PetyC/H7-Mode/2.Firmware/LVGL/CoreH7/import/WIFI_discon.png

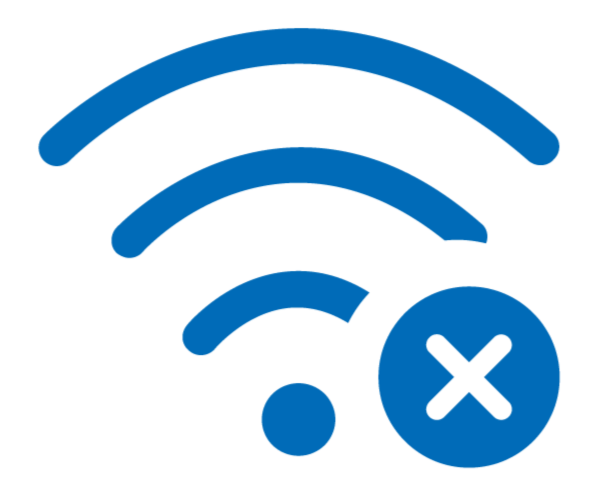
2.Firmware/LVGL/CoreH7/import/WIFI_discon.png
