PetyC/H7-Mode/1.Hardware/PCB_3D/STEP/1612_26MHZ.STEP

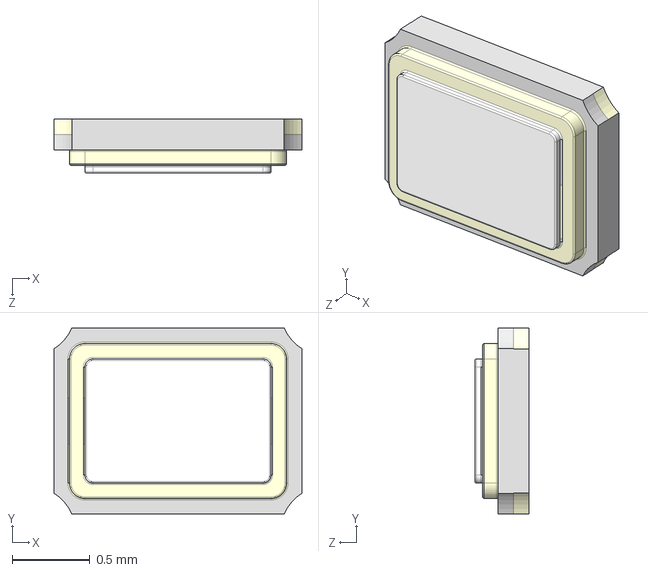
[picture p30: CAD file, 2022-08-18]
1.Hardware/PCB_3D/STEP/1612_26MHZ.STEP
1.60 x 1.20 x 0.35 mm
