PetyC/H7-Mode/1.Hardware/PCB_3D/STEP/MSK12C02.STEP

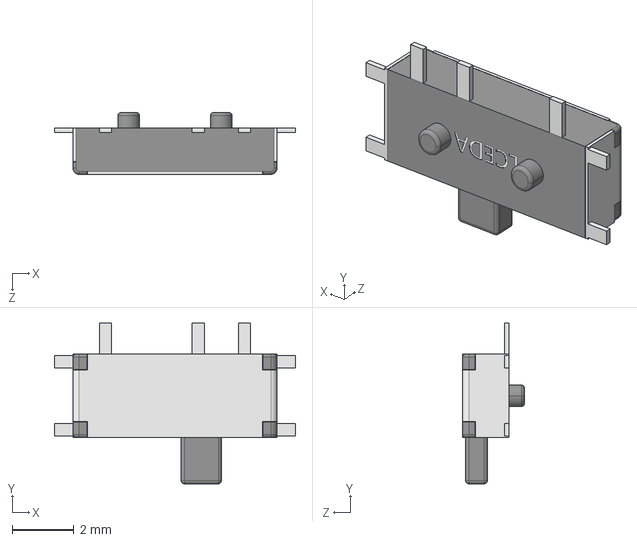
[picture p31: CAD file, 2022-08-18]
1.Hardware/PCB_3D/STEP/MSK12C02.STEP
7.80 x 5.20 x 2.00 mm
