PetyC/H7-Mode/1.Hardware/PCB_3D/STEP/K3-2410S-F1.STEP

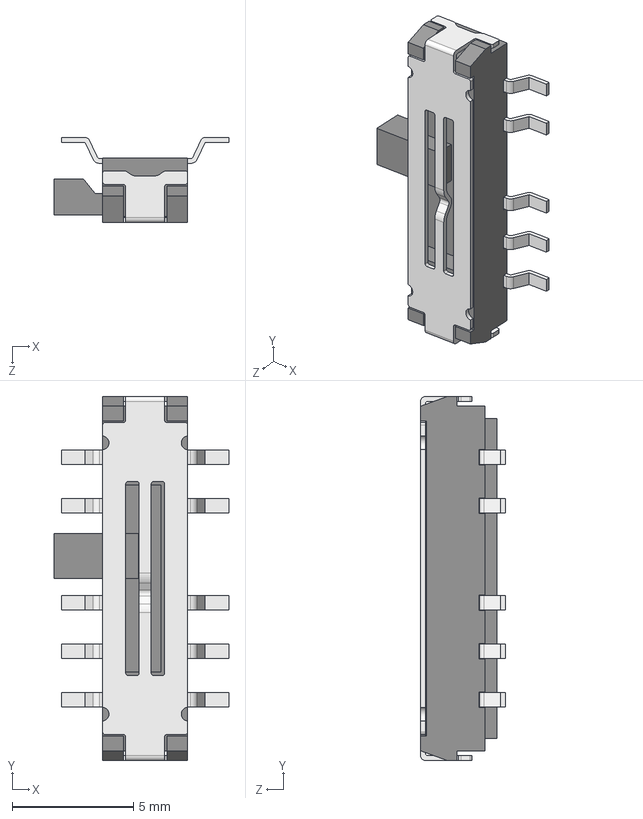
[picture p32: CAD file, 2022-08-18]
1.Hardware/PCB_3D/STEP/K3-2410S-F1.STEP
7.20 x 15.0 x 3.50 mm
