PetyC/H7-Mode/1.Hardware/PCB_3D/STEP/TM-2023.STEP

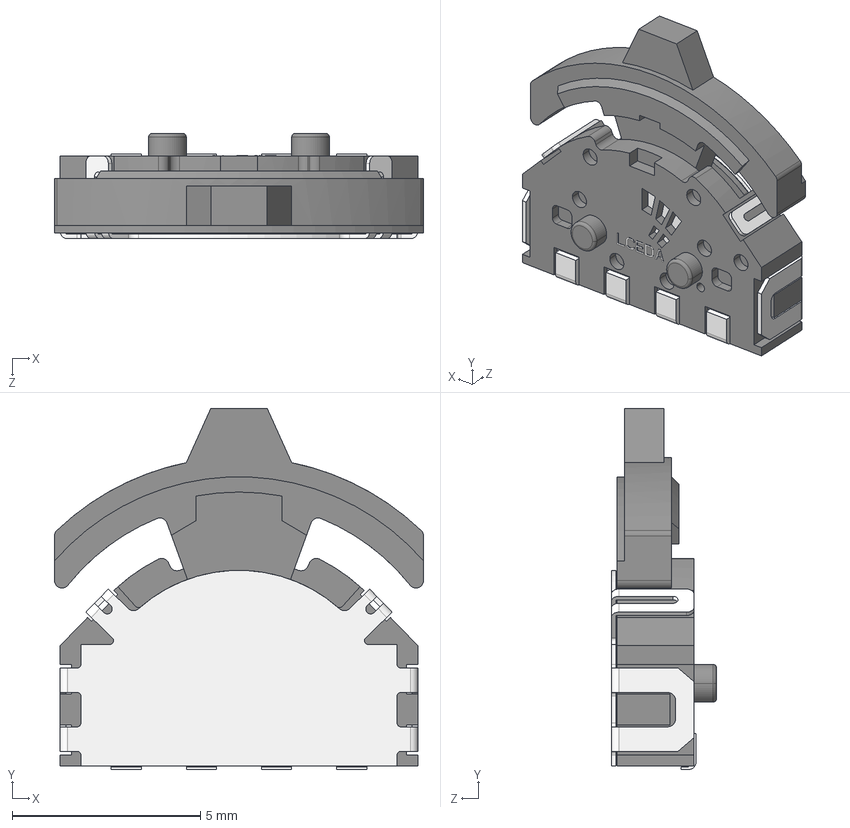
[picture p33: CAD file, 2022-08-18]
1.Hardware/PCB_3D/STEP/TM-2023.STEP
9.80 x 9.59 x 2.80 mm
