PetyC/H7-Mode/2.Firmware/STM32H743_FreeRTOS/User/Driver/src/Bsp_w25qxx.c

#include "Bsp_w25qxx.h"

/* 内部使用函数 */
static void QSPI_W25Qx_Write_Enable(QSPI_HandleTypeDef *hqspi);
static uint8_t QSPI_W25Qx_AutoPollingMemRead(QSPI_HandleTypeDef *hqspi);
static void Flash_Error_Handler(void);

/* 内部使用变量 */
struct 
{
  uint8_t CMD_Finished;     //命令发送状态 1:完成 0:未完成
  uint8_t RX_Finished;      //RX接受状态 1:完成 0:未完成
  uint8_t TX_Finished;      //TX发送状态 1:完成 0:未完成
  uint8_t Flash_Finished;   //FLASH状态 1:完成 0:未完成
}static __IO FLASH_Status;


/**
 * @brief 初始化W25QXX
 * @param {*}
 * @return {uint8_t} 0:成功  1:失败
 */
uint8_t QSPI_W25Qx_Init(void)
{	
	uint32_t FLASH_ID = 0;
	uint32_t FLASH_Type = 0;
	
	QSPI_W25Qx_Reset_Memory();
 
	FLASH_ID = QSPI_W25Qx_ReadID();
	FLASH_Type = QSPI_W25Qx_Read_Type();

	if(FLASH_ID == 0XEF4018 && FLASH_Type == 0XEF17)
	{
		return 0;
	}
	else
	{
		return 1;
	}
	
}


/**
 * @brief 读取外部FLASH的型号  (使用SPI模式的指令)
 * @param {*}
 * @return {uint32_t}  FLASH的ID
 */
uint32_t QSPI_W25Qx_Read_Type(void)
{
	uint32_t Type;

	QSPI_CommandTypeDef s_command = {0};
	uint8_t buf[3];

	/* 基本配置 */
	s_command.InstructionMode = QSPI_INSTRUCTION_1_LINE;	 // 1线方式发送指令
	s_command.AddressSize = QSPI_ADDRESS_24_BITS;			 // 24位地址
	s_command.AlternateByteMode = QSPI_ALTERNATE_BYTES_NONE; //无交替字节
	s_command.DdrMode = QSPI_DDR_MODE_DISABLE;				 // W25Q128JV不支持DDR模式
	s_command.DdrHoldHalfCycle = QSPI_DDR_HHC_ANALOG_DELAY;	 // DDR模式，数据输出延迟
	s_command.SIOOMode = QSPI_SIOO_INST_EVERY_CMD;			 //每次传输都发指令

	/* 读取JEDEC ID */
	s_command.Instruction = READ_ID_CMD; 	//读取命令: 0x90
	s_command.AddressMode = QSPI_ADDRESS_1_LINE; //没有地址
	s_command.DataMode = QSPI_DATA_1_LINE;	   // 1线数据
	s_command.DummyCycles = 0;				   //无空周期
	s_command.NbData = 2;					   //读取三个数据

	/* 发送指令 */
	if (HAL_QSPI_Command(&HQSPI_HANDLE, &s_command, HAL_QPSI_TIMEOUT_DEFAULT_VALUE) != HAL_OK)
	{
		Flash_Error_Handler();
	}

	/* 启动接收 */
	if (HAL_QSPI_Receive(&HQSPI_HANDLE, buf, HAL_QPSI_TIMEOUT_DEFAULT_VALUE) != HAL_OK)
	{
		Flash_Error_Handler();
	}

	Type = (buf[0] << 8) | buf[1];
	
	return Type;
}



/**
 * @brief 读取外部FLASH的ID  (使用SPI模式的指令)
 * @param {*}
 * @return {uint32_t}  FLASH的ID
 */
uint32_t QSPI_W25Qx_ReadID(void)
{
	uint32_t uiID;

	QSPI_CommandTypeDef s_command = {0};
	uint8_t buf[3];

	/* 基本配置 */
	s_command.InstructionMode = QSPI_INSTRUCTION_1_LINE;	 // 1线方式发送指令
	s_command.AddressSize = QSPI_ADDRESS_24_BITS;			 // 24位地址
	s_command.AlternateByteMode = QSPI_ALTERNATE_BYTES_NONE; //无交替字节
	s_command.DdrMode = QSPI_DDR_MODE_DISABLE;				 // W25Q128JV不支持DDR模式
	s_command.DdrHoldHalfCycle = QSPI_DDR_HHC_ANALOG_DELAY;	 // DDR模式，数据输出延迟
	s_command.SIOOMode = QSPI_SIOO_INST_EVERY_CMD;			 //每次传输都发指令

	/* 读取JEDEC ID */
	s_command.Instruction = READ_JEDEC_ID_CMD; //读取ID命令: 0x9F
	s_command.AddressMode = QSPI_ADDRESS_NONE; //没有地址
	s_command.DataMode = QSPI_DATA_1_LINE;	   // 1线数据
	s_command.DummyCycles = 0;				   //无空周期
	s_command.NbData = 3;					   //读取三个数据

	/* 发送指令 */
	if (HAL_QSPI_Command(&HQSPI_HANDLE, &s_command, HAL_QPSI_TIMEOUT_DEFAULT_VALUE) != HAL_OK)
	{
		Flash_Error_Handler();
	}

	/* 启动接收 */
	if (HAL_QSPI_Receive(&HQSPI_HANDLE, buf, HAL_QPSI_TIMEOUT_DEFAULT_VALUE) != HAL_OK)
	{
		Flash_Error_Handler();
	}

	uiID = (buf[0] << 16) | (buf[1] << 8) | buf[2];

	return uiID;
}

/**
 * @brief 复位外部Flash
 * @param {*}
 * @return {*}
 */
void QSPI_W25Qx_Reset_Memory(void)
{
	QSPI_CommandTypeDef s_command = {0};

	/* 基本配置 */
	s_command.InstructionMode = QSPI_INSTRUCTION_1_LINE;	 // 1线方式发送指令
	s_command.AddressSize = QSPI_ADDRESS_24_BITS;			 // 24位地址
	s_command.AlternateByteMode = QSPI_ALTERNATE_BYTES_NONE; //无交替字节
	s_command.DdrMode = QSPI_DDR_MODE_DISABLE;				 // W25Q128JV不支持DDR模式
	s_command.DdrHoldHalfCycle = QSPI_DDR_HHC_ANALOG_DELAY;	 // DDR模式，数据输出延迟
	s_command.SIOOMode = QSPI_SIOO_INST_EVERY_CMD;			 //每次传输都发指令

	/* 复位使能W25x */
	s_command.Instruction = RESET_ENABLE_CMD;  //复位使能命令
	s_command.AddressMode = QSPI_ADDRESS_NONE; //没有地址
	s_command.DataMode = QSPI_DATA_NONE;	   //没有数据
	s_command.DummyCycles = 0;				   //无空周期

	/* 发送复位使能命令 */
	if (HAL_QSPI_Command(&HQSPI_HANDLE, &s_command, HAL_QPSI_TIMEOUT_DEFAULT_VALUE) != HAL_OK)
	{
		Flash_Error_Handler();
	}

  /* 自动轮询模式等待等待完成 */
	if (QSPI_W25Qx_AutoPollingMemRead(&HQSPI_HANDLE) != HAL_OK)
	{
		Flash_Error_Handler();
	}

	/* 发送复位命令 */
	s_command.Instruction = RESET_MEMORY_CMD; //复位命令

	/* 发送复位使能命令 */
	if (HAL_QSPI_Command(&HQSPI_HANDLE, &s_command, HAL_QPSI_TIMEOUT_DEFAULT_VALUE) != HAL_OK)
	{
		Flash_Error_Handler();
	}

	/* 自动轮询模式等待等待完成 */
	if (QSPI_W25Qx_AutoPollingMemRead(&HQSPI_HANDLE) != HAL_OK)
	{
		Flash_Error_Handler();
	}
}

/**
 * @brief 擦除外部FLASH的扇区（大小：4KB)
 * @param {uint32_t} _sectorAddr 扇区地址，以4KB为单位的地址，比如0，4096，8192等
 * @return {*}
 */
void QSPI_W25Qx_EraseSector(uint32_t _sectorAddr)
{
	QSPI_CommandTypeDef s_command = {0};

	/* 写使能 */
	QSPI_W25Qx_Write_Enable(&HQSPI_HANDLE);

	/* 基本配置 */
	s_command.InstructionMode = QSPI_INSTRUCTION_1_LINE;	 // 1线方式发送指令
	s_command.AddressSize = QSPI_ADDRESS_24_BITS;			 // 24位地址
	s_command.AlternateByteMode = QSPI_ALTERNATE_BYTES_NONE; //无交替字节
	s_command.DdrMode = QSPI_DDR_MODE_DISABLE;				 // W25Q128JV不支持DDR模式
	s_command.DdrHoldHalfCycle = QSPI_DDR_HHC_ANALOG_DELAY;	 // DDR模式，数据输出延迟
	s_command.SIOOMode = QSPI_SIOO_INST_EVERY_CMD;			 //每次传输都发指令

	/* 擦除扇区配置 */
	s_command.Instruction = SECTOR_ERASE_CMD;	 //扇区擦除指令
	s_command.AddressMode = QSPI_ADDRESS_1_LINE; // 1线地址方式
	s_command.DataMode = QSPI_DATA_NONE;		 //没有数据
	s_command.Address = _sectorAddr;			 //扇区的首地址，保证是4KB整数倍
	s_command.DummyCycles = 0;					 //无空周期

 
  FLASH_Status.CMD_Finished = 0;

	/* 发送指令 */
	if (HAL_QSPI_Command_IT(&HQSPI_HANDLE, &s_command) != HAL_OK)
	{
		Flash_Error_Handler();
	}

	/* 等待命令发送完毕 */
	while (FLASH_Status.CMD_Finished == 0);
	FLASH_Status.CMD_Finished = 0;

	/* 等待擦写结束 */
	FLASH_Status.Flash_Finished = 0;
	QSPI_W25Qx_AutoPollingMemRead(&HQSPI_HANDLE);
	while (FLASH_Status.Flash_Finished == 0);
	FLASH_Status.Flash_Finished = 0;

	
}

/**
 * @brief 擦除整个芯片
 * @return {*}
 */
void QSPI_W25Qx_EraseChip(void)
{
	QSPI_CommandTypeDef s_command = {0};

	/* 写使能 */
	QSPI_W25Qx_Write_Enable(&HQSPI_HANDLE);

	/* 基本配置 */
	s_command.InstructionMode = QSPI_INSTRUCTION_1_LINE;	 // 1线方式发送指令
	s_command.AddressSize = QSPI_ADDRESS_24_BITS;			 // 24位地址
	s_command.AlternateByteMode = QSPI_ALTERNATE_BYTES_NONE; //无交替字节
	s_command.DdrMode = QSPI_DDR_MODE_DISABLE;				 // W25Q128JV不支持DDR模式
	s_command.DdrHoldHalfCycle = QSPI_DDR_HHC_ANALOG_DELAY;	 // DDR模式，数据输出延迟
	s_command.SIOOMode = QSPI_SIOO_INST_EVERY_CMD;			 //每次传输都发指令

	/* 擦除扇区配置 */
	s_command.Instruction = SECTOR_CHIP_CMD;	 //擦除整个芯片指令
	s_command.AddressMode = QSPI_ADDRESS_1_LINE; // 1线地址方式
	s_command.DataMode = QSPI_DATA_NONE;		 //没有数据
	s_command.Address = 0;			            //没有地址
	s_command.DummyCycles = 0;					 //无空周期

 
  FLASH_Status.CMD_Finished = 0;

	/* 发送指令 */
	if (HAL_QSPI_Command_IT(&HQSPI_HANDLE, &s_command) != HAL_OK)
	{
		Flash_Error_Handler();
	}

	/* 等待命令发送完毕 */
	while (FLASH_Status.CMD_Finished == 0);
	FLASH_Status.CMD_Finished = 0;

	/* 等待擦写结束 */
	FLASH_Status.Flash_Finished = 0;
	QSPI_W25Qx_AutoPollingMemRead(&HQSPI_HANDLE);
	while (FLASH_Status.Flash_Finished == 0);
	FLASH_Status.Flash_Finished = 0;

	
}


/**
 * @brief 连续读取若干字节，字节的个数不能超出芯片容量  (从SPI模式切换到QSPI模式，读取完毕后切换回SPI模式（其他函数仅仅支持SPI模式）。)
 * @param {uint8_t} *_pBuf 读取数据的存放地址
 * @param {uint32_t} _read_Addr 起始的地址
 * @param {uint32_t} _read_Size  数据个数，可以大于W25Q128JV_PAGE_SIZE,但不能超出芯片总容量
 * @return {*}
 */
void QSPI_W25Qx_Read_Buffer(uint32_t _read_Addr , uint8_t *_pBuf, uint32_t _read_Size)
{
	QSPI_CommandTypeDef s_command = {0};

	/* 开始从FLASH读取数据 */
	/* 基本配置 */
	s_command.InstructionMode = QSPI_INSTRUCTION_1_LINE;	 // 1线方式发送指令
	s_command.AddressSize = QSPI_ADDRESS_24_BITS;			 // 24位地址
	s_command.AlternateByteMode = QSPI_ALTERNATE_BYTES_NONE; //无交替字节
	s_command.DdrMode = QSPI_DDR_MODE_DISABLE;				 // W25Q128JV不支持DDR模式
	s_command.DdrHoldHalfCycle = QSPI_DDR_HHC_ANALOG_DELAY;	 // DDR模式，数据输出延迟
	s_command.SIOOMode = QSPI_SIOO_INST_EVERY_CMD;			 //每次传输都发指令

	/*读取序列配置 */
	s_command.Instruction = QUAD_INOUT_FAST_READ_CMD;    // 四线快速读出指令
	s_command.AddressMode = QSPI_ADDRESS_4_LINES;	       // 4线地址方式
	s_command.DataMode = QSPI_DATA_4_LINES;			         // 4线数据方式
	s_command.Address = _read_Addr;					             //写入数据的地址
	s_command.NbData = _read_Size;					             //写入数据的大小
	s_command.DummyCycles = 6;						               //空闲状态周期

	/* 发送指令 */
	if (HAL_QSPI_Command(&HQSPI_HANDLE, &s_command, HAL_QPSI_TIMEOUT_DEFAULT_VALUE) != HAL_OK)
	{
		Flash_Error_Handler();
	}

  FLASH_Status.RX_Finished = 0;

	//读取数据（DMA方式） 
	if (HAL_QSPI_Receive_DMA(&HQSPI_HANDLE, _pBuf) != HAL_OK) 
	{
		Flash_Error_Handler();
	}

	//等待DMA读取完毕 
	while ( FLASH_Status.RX_Finished == 0);
	FLASH_Status.RX_Finished = 0;

}

/**
 * @brief 页编程，通过QSPI将数据写入外部FALSH
 * @param {uint8_t} *_pBuf 需要存入数据的指针
 * @param {uint32_t} _write_Addr 目标区域首地址，即页首地址，比如0，256，512等。
 * @param {uint16_t} _write_Size 数据个数，不能超过页的大小，可以填入（1 ~ 256）
 * @return {uint8_t}
 */
uint8_t QSPI_W25Qx_Write_Buffer(uint32_t _write_Addr ,uint8_t *_pBuf, uint16_t _write_Size)
{
	QSPI_CommandTypeDef s_command = {0};

	/* 防止写入的大小超过256字节 */
	if (_write_Size > QSPI_PAGE_SIZE)
	{
		/* 进入断言，提示错误 */
		Flash_Error_Handler();
	}

	QSPI_W25Qx_Write_Enable(&HQSPI_HANDLE); //写使能

	/* 基本配置 */
	s_command.InstructionMode = QSPI_INSTRUCTION_1_LINE;	 // 1线方式发送指令
	s_command.AddressSize = QSPI_ADDRESS_24_BITS;			 // 24位地址
	s_command.AlternateByteMode = QSPI_ALTERNATE_BYTES_NONE; //无交替字节
	s_command.DdrMode = QSPI_DDR_MODE_DISABLE;				 // W25Q128JV不支持DDR模式
	s_command.DdrHoldHalfCycle = QSPI_DDR_HHC_ANALOG_DELAY;	 // DDR模式，数据输出延迟
	s_command.SIOOMode = QSPI_SIOO_INST_EVERY_CMD;			 //每次传输都发指令

	/*写入序列配置 */
	s_command.Instruction = QUAD_INPUT_PAGE_PROG_CMD; // 四线快速写入指令
	s_command.AddressMode = QSPI_ADDRESS_1_LINE;	  // 1线地址方式
	s_command.DataMode = QSPI_DATA_4_LINES;			  // 4线数据方式
	s_command.Address = _write_Addr;				  //写入数据的地址
	s_command.NbData = _write_Size;					  //写入数据的大小
	s_command.DummyCycles = 0;						  //无空周期

	/* 发送指令 */
	if (HAL_QSPI_Command(&HQSPI_HANDLE, &s_command, HAL_QPSI_TIMEOUT_DEFAULT_VALUE) != HAL_OK)
	{
		Flash_Error_Handler();
	}

  FLASH_Status.TX_Finished = 0;
	FLASH_Status.Flash_Finished = 0;

	//启动传输
	if (HAL_QSPI_Transmit_DMA(&HQSPI_HANDLE, _pBuf) != HAL_OK)
	{
		Flash_Error_Handler();
	}

	//等待发送完毕 
	while (FLASH_Status.TX_Finished == 0);
	FLASH_Status.TX_Finished = 0;

	//等待写入结束 
	QSPI_W25Qx_AutoPollingMemRead(&HQSPI_HANDLE);
	while (FLASH_Status.Flash_Finished == 0);
	FLASH_Status.Flash_Finished = 0;


	return 0;
}



/**
 * @brief 外部FLASH写使能 (使用SPI模式的指令)
 * @param {QSPI_HandleTypeDef} *hqspi
 * @return {*}
 */
static void QSPI_W25Qx_Write_Enable(QSPI_HandleTypeDef *hqspi)
{
	QSPI_CommandTypeDef s_command = {0};

	/* 基本配置 */
	s_command.InstructionMode = QSPI_INSTRUCTION_1_LINE; // 1线方式发送指令
	s_command.AddressSize = QSPI_ADDRESS_24_BITS;       //24位地址
	s_command.AlternateByteMode = QSPI_ALTERNATE_BYTES_NONE; //无交替字节
	s_command.DdrMode = QSPI_DDR_MODE_DISABLE;				 // W25Q128JV不支持DDR模式
	s_command.DdrHoldHalfCycle = QSPI_DDR_HHC_ANALOG_DELAY;	 // DDR模式，数据输出延迟
	s_command.SIOOMode = QSPI_SIOO_INST_EVERY_CMD;			 //每次传输都发指令

	/* 写入使能配置 */
	s_command.Instruction = WRITE_ENABLE_CMD;  //写使能命令 
	s_command.AddressMode = QSPI_ADDRESS_NONE; //没有地址
	s_command.DataMode = QSPI_DATA_NONE;	   //没有数据
	s_command.DummyCycles = 0;				   //无空周期
	s_command.NbData = 0;					   //空数据


	if (HAL_QSPI_Command(hqspi, &s_command , HAL_QPSI_TIMEOUT_DEFAULT_VALUE) != HAL_OK)
	{
		Flash_Error_Handler();
	}

}


/**
 * @brief 等待QSPI Flash就绪
 * @param {uint32_t} Timeout   超时时间
 * @return {uint8_t}Flash的状态
 */
static uint8_t QSPI_W25Qx_AutoPollingMemRead(QSPI_HandleTypeDef *hqspi)
{
	QSPI_CommandTypeDef s_command = {0};
	QSPI_AutoPollingTypeDef s_config = {0};

	/* 基本配置 */
	s_command.InstructionMode = QSPI_INSTRUCTION_1_LINE;	 // 1线方式发送指令
	s_command.AddressSize = QSPI_ADDRESS_24_BITS;			 // 24位地址
	s_command.AlternateByteMode = QSPI_ALTERNATE_BYTES_NONE; //无交替字节
	s_command.DdrMode = QSPI_DDR_MODE_DISABLE;				 // W25Q128JV不支持DDR模式
	s_command.DdrHoldHalfCycle = QSPI_DDR_HHC_ANALOG_DELAY;	 // DDR模式，数据输出延迟
	s_command.SIOOMode = QSPI_SIOO_INST_EVERY_CMD;			 //每次传输都发指令

	/* 配置自动轮询模式 */
	s_command.Instruction = READ_STATUS_REG1_CMD; //读取状态寄存器
	s_command.AddressMode = QSPI_ADDRESS_NONE;	  //没有地址
	s_command.DataMode = QSPI_DATA_1_LINE;		  // 1线数据
	s_command.DummyCycles = 0;					  //无空周期

	/* 配置自动轮询寄存器（不断查询状态寄存器bit0，等待其为0） */
	s_config.Match = 0x00;					  //等待其为0
	s_config.Mask = W25Q128JV_FSR_BUSY;		  //状态寄存器bit0
	s_config.MatchMode = QSPI_MATCH_MODE_AND; //逻辑与
	s_config.StatusBytesSize = 1;
	s_config.Interval = 0x10;
	s_config.AutomaticStop = QSPI_AUTOMATIC_STOP_ENABLE;

	/* 自动轮询模式等待编程结束 */
	if (HAL_QSPI_AutoPolling_IT(hqspi, &s_command, &s_config) != HAL_OK)
	{
		Flash_Error_Handler();
	}


	return 0;
}

/**
 * @brief QSPI命令完成中断回调函数，
 * @param {QSPI_HandleTypeDef} *hqspi
 * @return {*}
 */
void HAL_QSPI_CmdCpltCallback(QSPI_HandleTypeDef *hqspi)
{
	FLASH_Status.CMD_Finished = 1;
}

/**
 * @brief QSPI接收完成中断回调函数
 * @param {*}
 * @return {*}
 */
void HAL_QSPI_RxCpltCallback(QSPI_HandleTypeDef *hqspi)
{
	FLASH_Status.RX_Finished++;
}

/**
 * @brief  QSPI发送完成中断回调函数
 * @param {QSPI_HandleTypeDef} *hqspi
 * @return {*}
 */
void HAL_QSPI_TxCpltCallback(QSPI_HandleTypeDef *hqspi)
{
	FLASH_Status.TX_Finished = 1;
}

/**
 * @brief QSPI状态匹配回调中断回调函数
 * @param {QSPI_HandleTypeDef} *hqspi
 * @return {*}
 */
void HAL_QSPI_StatusMatchCallback(QSPI_HandleTypeDef *hqspi)
{
	FLASH_Status.Flash_Finished = 1;
}

/**
 * @brief 当FLASH发生错误时进入
 * @param {*}
 * @return {*}
 */
static void Flash_Error_Handler(void)
{
	__disable_irq();
	while (1)
	{
	}
}


#if 1
#include "Bsp_Uart.h"

struct 
{
  double Write_Speed;
  double Write_Time;
  double Read_Speed;
  double Read_Time;
  double Erase_Speed;
  double Erase_Time;
}QSPI_FLASH_TestInfo;

#define FLASH_SPEED_TEST_SIZE (64*1024)
uint8_t Flash_Speed_TestBuf[FLASH_SPEED_TEST_SIZE];

void QSPI_FLASH_Test_ReadSpeed(void)
{ 

  char buff[] = "QSPI FLASH速度测试开始\r\n"; 
  Bsp_UART_Write(&huart1 , (uint8_t *)buff , sizeof(buff));
  Bsp_UART_Poll_DMA_TX(&huart1);


  memset(Flash_Speed_TestBuf , 0x55 , FLASH_SPEED_TEST_SIZE);
  QSPI_FLASH_TestInfo.Read_Speed = 0;
  QSPI_FLASH_TestInfo.Read_Time = 0;

  uint32_t Tick_0 = 0;
  uint32_t Tick_1 = 0;

  /*擦除测试*/
  __set_PRIMASK(1);
  Tick_0 = HAL_GetTick();
  __set_PRIMASK(0);

  for (uint32_t Addr = 0; Addr < FLASH_SPEED_TEST_SIZE; Addr += 4096)
  {
    QSPI_W25Qx_EraseSector(Addr);
  }
 
  __set_PRIMASK(1);
  Tick_1 = HAL_GetTick();
  __set_PRIMASK(0);

  QSPI_FLASH_TestInfo.Erase_Time = Tick_1 - Tick_0;
  QSPI_FLASH_TestInfo.Erase_Speed = FLASH_SPEED_TEST_SIZE / (QSPI_FLASH_TestInfo.Erase_Time);



  /*写入测试*/
  __set_PRIMASK(1);
  Tick_0 = HAL_GetTick();
  __set_PRIMASK(0);

  for (uint32_t Addr = 0; Addr < FLASH_SPEED_TEST_SIZE; Addr += 256)
	{
		QSPI_W25Qx_Write_Buffer(Addr ,&Flash_Speed_TestBuf[Addr] , 256 ); 
	}

  __set_PRIMASK(1);
  Tick_1 = HAL_GetTick();
  __set_PRIMASK(0);

  QSPI_FLASH_TestInfo.Write_Time = Tick_1 - Tick_0;
  QSPI_FLASH_TestInfo.Write_Speed = FLASH_SPEED_TEST_SIZE/ (QSPI_FLASH_TestInfo.Write_Time);


  /*读取测试*/
  __set_PRIMASK(1);
  Tick_0 = HAL_GetTick();
 __set_PRIMASK(0);

	for (uint32_t Addr = 0; Addr < QSPI_FLASH_SIZE; Addr += FLASH_SPEED_TEST_SIZE)
	{
		QSPI_W25Qx_Read_Buffer(Addr, Flash_Speed_TestBuf , FLASH_SPEED_TEST_SIZE);
	}
	
  __set_PRIMASK(1);
  Tick_1 = HAL_GetTick();
  __set_PRIMASK(0);

  QSPI_FLASH_TestInfo.Read_Time = Tick_1 - Tick_0;
  QSPI_FLASH_TestInfo.Read_Speed = QSPI_FLASH_SIZE/ (QSPI_FLASH_TestInfo.Read_Time);


  char TX_Buff[512] = {0};

  uint16_t Tx_Buff_Len = sprintf(TX_Buff , "擦除总数:%d字节\t擦除总用时:%.2fms\t擦除速度:%.2fKb/s\r\n" , (int)(FLASH_SPEED_TEST_SIZE) , QSPI_FLASH_TestInfo.Erase_Time , QSPI_FLASH_TestInfo.Erase_Speed);
  Tx_Buff_Len += sprintf(&TX_Buff[Tx_Buff_Len] , "写入总数:%.d字节\t写入总用时:%.2fms\t写入速度:%.2fKb/s\r\n" , (int)(FLASH_SPEED_TEST_SIZE) , QSPI_FLASH_TestInfo.Write_Time , QSPI_FLASH_TestInfo.Write_Speed );
  sprintf(&TX_Buff[Tx_Buff_Len] , "读取总数:%d字节\t读取总用时:%.2fms\t读取速度:%.2fKb/s\r\n" , (int)(QSPI_FLASH_SIZE) , QSPI_FLASH_TestInfo.Read_Time , QSPI_FLASH_TestInfo.Read_Speed);

  Bsp_UART_Write(&huart1 , (uint8_t *)TX_Buff , sizeof(TX_Buff));
  Bsp_UART_Poll_DMA_TX(&huart1);

  return;
}
#endif
   
