PetyC/H7-Mode/2.Firmware/STM32H743_FatFs/User/Dev_Uart/CRC.c

#include "CRC.h"


/**
* @brief calculate CRC 计算CRC
* @param *modbusdata: Source data address
* @param length: data length
* @param
* @retval CRC16 Value
* @example
**/
uint16_t crc16_modbus(uint8_t *modbusdata, uint16_t length)
{
 
  int crc = 0xffff;	//0xffff or 0
  for (uint16_t i = 0; i < length; i++)
  {
    crc ^= modbusdata[i];
		
    for (uint16_t j = 0; j < 8; j++)
    {
      if ((crc & 0x01) == 1)
      {
        crc = (crc >> 1) ^ 0xa001;
      }
      else
      {
        crc >>= 1;
      }
    }
}
  return crc;
}


/**
* @brief check CRC for data 判断接收的数据CRC是否正确
* @param *modbusdata: Read data address
* @param length: Read data length
* @param
* @retval 1:CRC16 OK
* @example
**/
uint16_t crc16_flage(uint8_t *modbusdata, int length)
{
  uint16_t Receive_CRC = 0, calculation = 0;

  if(length<=2)
  {
    return 0;
  }

  Receive_CRC = crc16_modbus(modbusdata, length-4);

  calculation = modbusdata[length-4];

  calculation <<= 8;

  calculation += modbusdata[length-3];

  if(calculation != Receive_CRC)
  {
    return 0;
  }

  return 1;
}
/*
///////////////////////////////
//查表法
///////////////////////////////
const char crctableh[] = {
    0x00, 0xC1, 0x81, 0x40, 0x01, 0xC0, 0x80, 0x41, 0x01, 0xC0, 0x80, 0x41, 0x00, 0xC1, 0x81,
    0x40, 0x01, 0xC0, 0x80, 0x41, 0x00, 0xC1, 0x81, 0x40, 0x00, 0xC1, 0x81, 0x40, 0x01, 0xC0,
    0x80, 0x41, 0x01, 0xC0, 0x80, 0x41, 0x00, 0xC1, 0x81, 0x40, 0x00, 0xC1, 0x81, 0x40, 0x01,
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
{
    uint8_t crch = 0xff;
    uint8_t crcl = 0xff; 
    uint32_t index;
    while (length--) 
    {
        index = crcl ^ *modbusdata++; 
        crcl = crch ^ crctableh[index];
        crch = crctablel[index];
    }
    return (crch << 8 | crcl);
}
*/
