PetyC/H7-Mode/2.Firmware/STM32H743_FreeRTOS/User/APP/Network_Task.h

/*
 * @Description: NetWork相关
 * @Autor: Pi
 * @Date: 2022-08-08 18:24:22
 * @LastEditTime: 2022-08-31 13:55:32
 */
 
#ifndef NETWORK_TASK_H
#define NETWORK_TASK_H


/*FreeRTOS相关头文件*/
#include "FreeRTOS.h"
#include "task.h"
#include "cmsis_os.h"
#include "limits.h"

/*任务通知*/
#define NETWORK_WIFI_BIT0  (1ul)
#define NETWORK_CONNECT_BIT0  (1ul << 1)



/*相关微库*/
#include "string.h"
#include "stdio.h"

/*BSP相关文件*/
#include "main.h"
#include "Bsp_ESP8266.h"
#include "Bsp_ESP8266_Network.h"

void Network_Task(void const * argument);



#endif
