PetyC/H7-Mode/2.Firmware/STM32H743_FreeRTOS/User/Driver/include/Bsp_ESP8266_Network.h

/*
 * @Description: 
 * @Autor: Pi
 * @Date: 2022-08-05 21:54:16
 * @LastEditTime: 2022-09-05 03:15:19
 */
#ifndef BSP_ESP8266_NETWORK_H
#define BSP_ESP8266_NETWORK_H

#include "main.h"
#include "BSP_ESP8266_cString.h"
#include "Bsp_ESP8266.h"

/*Station信息*/
typedef struct 
{
  char ssid[33];
  char pwd[20];
}WIFI_Station_T;


/*连接状态*/
typedef enum 
{
  Link = 2,
  UnLink = 5,
  NetLink = 3,
  UnNetLink = 4,
}AP_Connect_E;

 
/*网络相关结构体*/
typedef struct 
{
  WIFI_Station_T AP;
  AP_Connect_E AP_Connect;
}Network_T;


extern Network_T Network;

void NetWork_Init(void);
uint8_t NetWork_APUconfig(void);
uint8_t NetWork_QueryLink(void);









#endif
