PetyC/H7-Mode/2.Firmware/STM32H743_FreeRTOS/User/Driver/include/Bsp_st7735s.h

/*
 * @Description: 
 * @Autor: Pi
 * @Date: 2022-08-22 17:12:15
 * @LastEditTime: 2022-09-01 03:00:45
 */
#ifndef BSP_ST7735S_H_
#define BSP_ST7735S_H_

#include "Bsp_st7735s_interface.h"


/*LCD功能设置*/
void LCD_Init(void);
void LCD_Reset(void);
void LCD_BacklightPct(uint8_t pct);


/*绘图功能*/
void LCD_SetRegion(uint16_t x_start, uint16_t y_start, uint16_t x_end, uint16_t y_end);
void LCD_SetXY(uint16_t x, uint16_t y);
void LCD_DrawPoint(uint16_t x, uint16_t y, uint16_t Data);
void LCD_FullColor(uint16_t Color);
void LCD_DisplayImages(uint16_t *Images);
void LCD_FillColor(uint16_t x_start, uint16_t y_start, uint16_t x_end, uint16_t y_end , uint16_t *data);
void LCD_FillColor_DMA(uint16_t x_start, uint16_t y_start, uint16_t x_end, uint16_t y_end, uint16_t *data);
#endif
