PetyC/H7-Mode/2.Firmware/STM32H743_Bootloader/User/App/Uart_process/app_uart.h

/*
 * @Description: 串口数据处理
 * @Autor: Pi
 * @Date: 2022-07-04 19:10:39
 * @LastEditTime: 2022-07-20 17:37:25
 */
#ifndef APP_UART_H
#define APP_UART_H

#include "Bsp_Uart.h"


extern void (*User_UART_RX_Fun)(uint8_t *data, uint16_t len);                           //串口接收数据处理函数指针
extern void (*User_UART_RX_Finished)(uint8_t *data, uint16_t len);                      //串口接收数据处理完成函数指针
extern void (*User_UART_RX_None)(void);                                                 //串口无数据

/*数据处理状态机 循环调用*/
void User_UART_RX_Loop(void);

/*设置从串口读取数据长度最大值*/
void User_UART_RX_Size_Max(uint16_t Size);

/*单帧最短长度*/
void User_UART_RX_Overflow_Max(uint16_t Size);

/*设置串口超时最大时间 默认5ms*/
void User_Uart_RX_Timeout_Set(uint16_t Timeout);

/*定时中断服务函数*/
void User_UART_Timer(void);



/************************测试用函数********************/
/*串口回显功能*/
void User_UART_Echo(uint8_t *data , uint16_t len);

/*串口接收完成 测试用*/
void User_UART_Finished_Demo(uint8_t *data, uint16_t len);

/*将FIFO中的数据循环发送出去*/
void User_UART_TX_Loop(void);

/*串口发送中断服务函数*/
void User_UART_TX_Timer(void);
#endif
